catalin-giuglan/Proiect_TSC/Images/OpenBook Enclosure v11.png

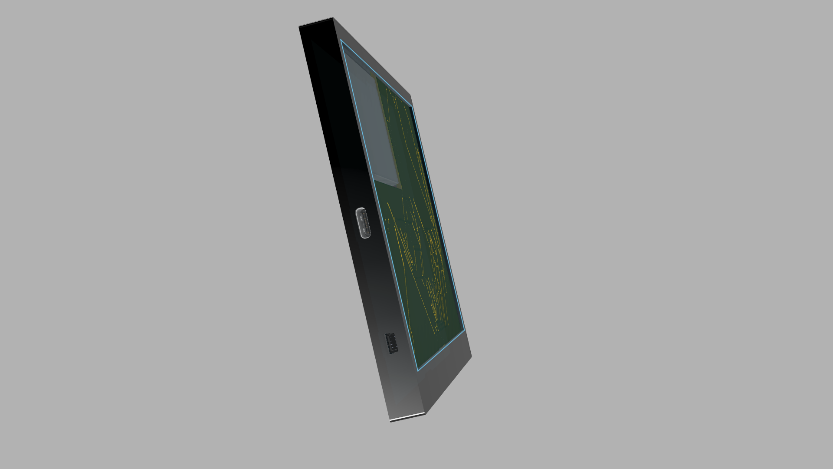
Images/OpenBook Enclosure v11.png
