catalin-giuglan/Proiect_TSC/Images/OpenBook Enclosure v12.png

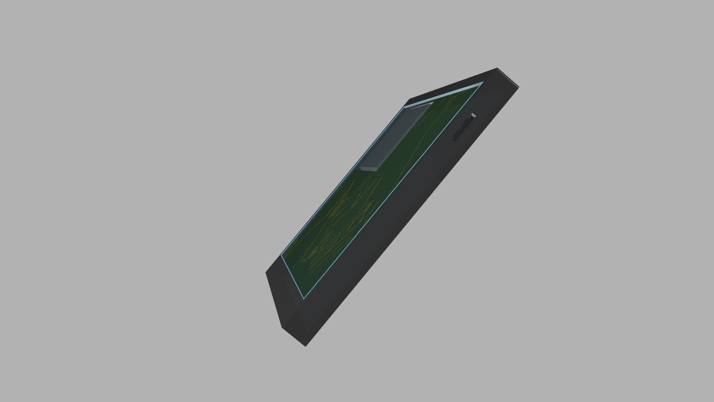
Images/OpenBook Enclosure v12.png
