catalin-giuglan/Proiect_TSC/Images/PCB_Top.png

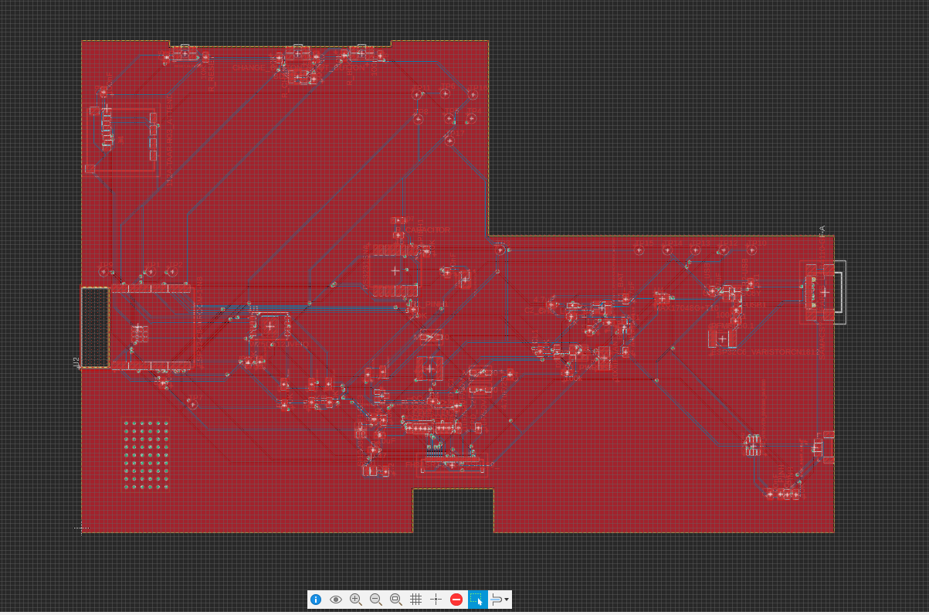
Images/PCB_Top.png
