catalin-giuglan/Proiect_TSC/Images/Project.png

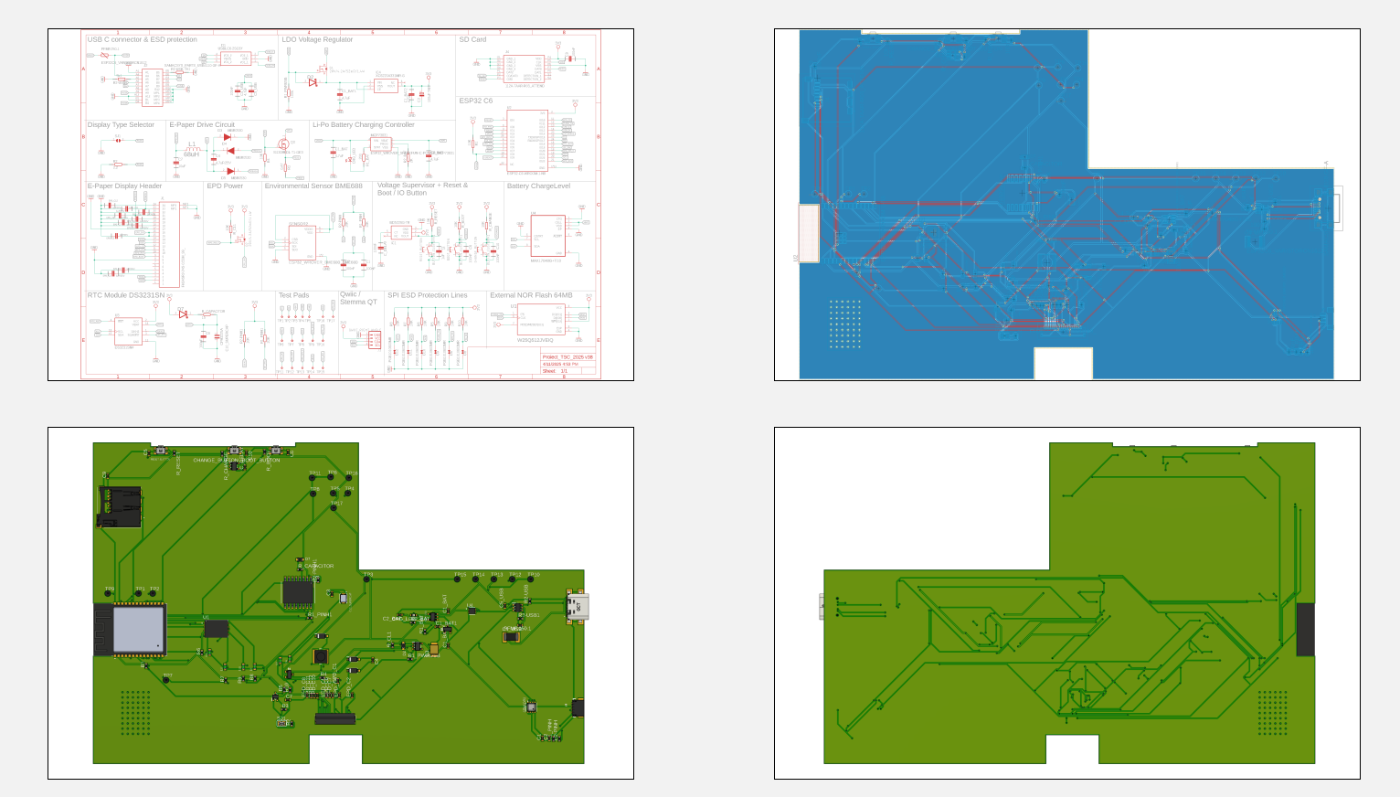
Images/Project.png
